whomble/arduino_sunrise_clock/img/IMG_20190324_202402.jpg

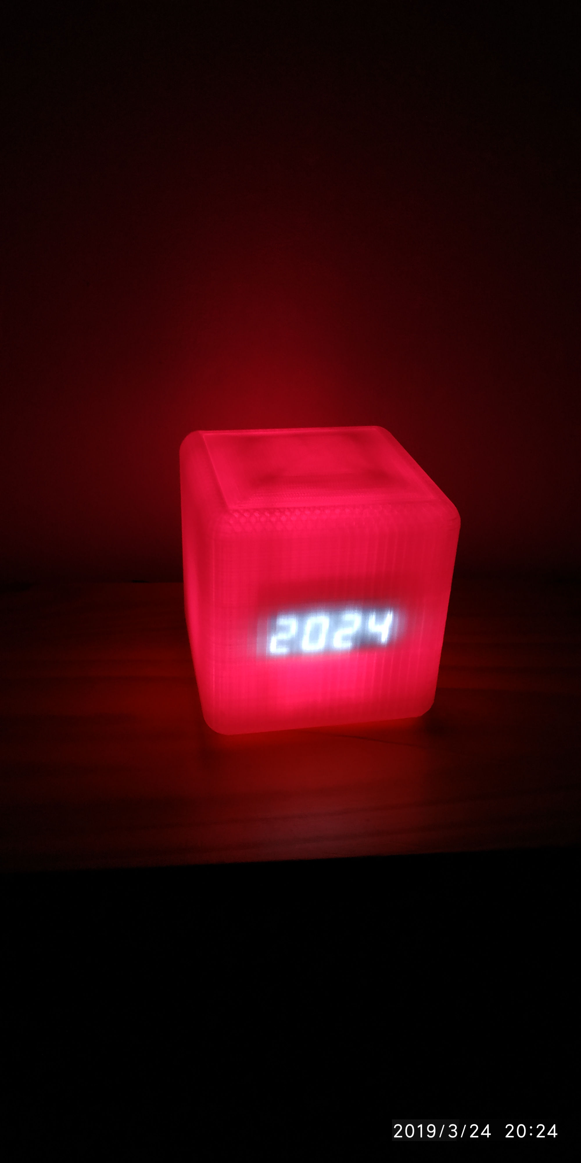
img/IMG_20190324_202402.jpg
