whomble/arduino_sunrise_clock/img/IMG_20190325_081732.jpg

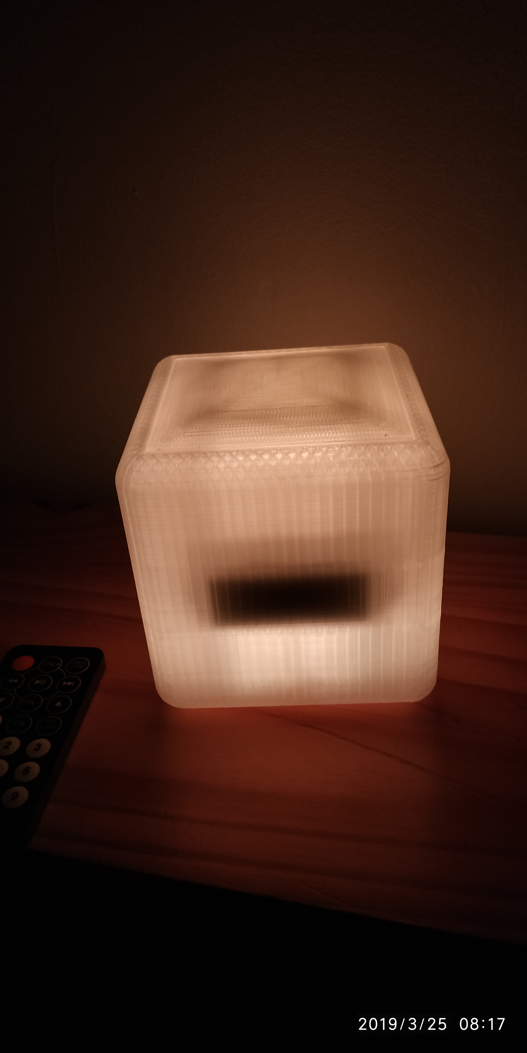
img/IMG_20190325_081732.jpg
