whomble/arduino_sunrise_clock/img/IMG_20190325_081749.jpg

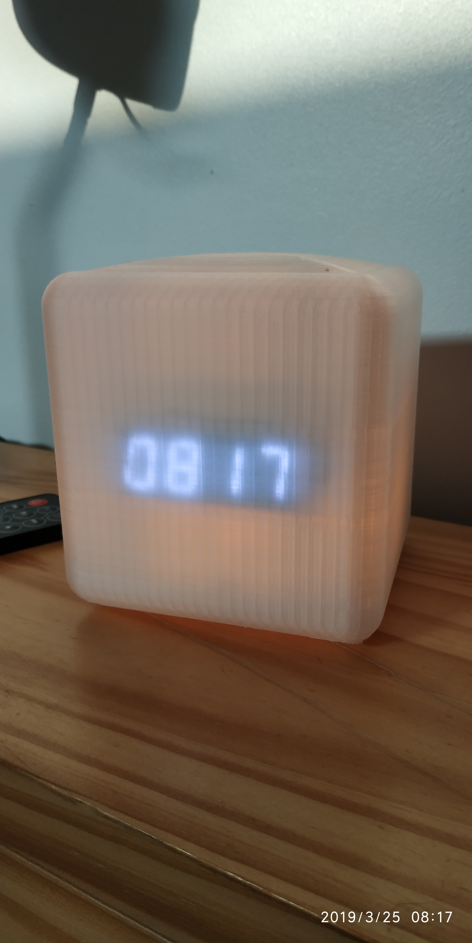
img/IMG_20190325_081749.jpg
