whomble/arduino_sunrise_clock/img/IMG_20221128_103421.jpg

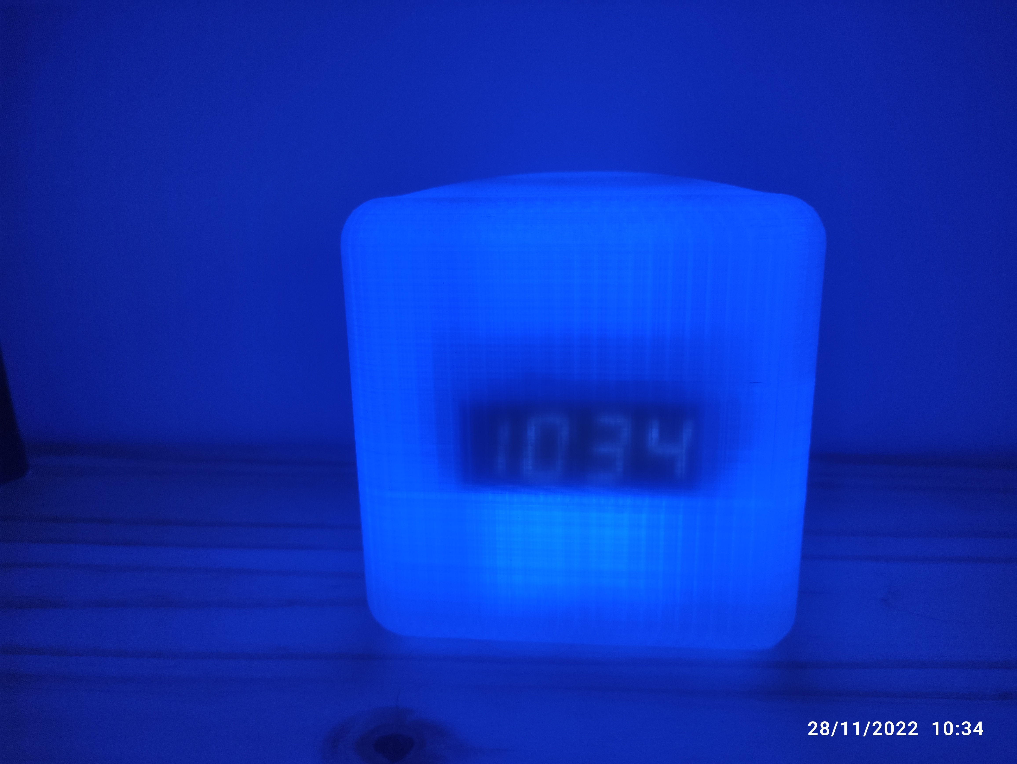
img/IMG_20221128_103421.jpg
